PratikGupta114/Glider/Code_examples/Glider_v1.0/PlatformIO_projects/Line_Follower_Robot/src/Sensor.cpp

#include <stdint.h>
#include <stdbool.h>
#include <Arduino.h>

#include "GlobalVariables.h"
#include "PinDefinitions.h"
#include "Config.h"
#include "Wire.h"

bool sensorInitialized = false;

uint8_t shiftIn165(gpio_num_t dataPin, gpio_num_t clockPin, uint8_t bitOrder)
{
    uint8_t value = 0;
    uint8_t i;

    for (i = 0; i < 8; ++i)
    {
        uint8_t r = gpio_get_level(dataPin);
        if (bitOrder == LSBFIRST)
            value |= r << i;
        else
            value |= r << (7 - i);
        gpio_set_level(clockPin, 1);
        gpio_set_level(clockPin, 0);
    }

    return value;
}

uint8_t horizontalFlip(uint8_t byte)
{
    uint8_t flippedByte = 0x00;
    for (int i = 0; i < 4; i++)
    {
        uint8_t bs = (byte >> i) & 0x01;
        uint8_t be = (byte >> (7 - i)) & 0x01;
        flippedByte |= (bs << (7 - i)) | (be << i);
    }
    return flippedByte;
}

uint16_t getProcessedSensorData(uint8_t leftHalfPinState, uint8_t rightHalfPinState)
{
    leftHalfPinState = horizontalFlip(leftHalfPinState);
    rightHalfPinState = horizontalFlip(rightHalfPinState);

    uint16_t processedSensorData = leftHalfPinState << 8 | rightHalfPinState;

    return processedSensorData;
}

// returns a 2-byte data where each bit represent the state of each sensor
uint16_t getSensorReadings()
{
    uint16_t reading = 0x0000;

    if (!sensorInitialized)
    {
        gpio_config_t io_config;
        io_config.pin_bit_mask = (1 << DATA_PIN);
        io_config.mode = GPIO_MODE_INPUT;
        io_config.pull_up_en = GPIO_PULLUP_ENABLE;
        io_config.pull_down_en = GPIO_PULLDOWN_DISABLE;
        io_config.intr_type = GPIO_INTR_DISABLE;
        gpio_config(&io_config);

        io_config.pin_bit_mask = (1 << CLOCK_PIN | 1 << CLOCK_ENABLE_PIN | 1 << LOAD_PIN);
        io_config.mode = GPIO_MODE_OUTPUT;
        io_config.pull_up_en = GPIO_PULLUP_DISABLE;
        io_config.pull_down_en = GPIO_PULLDOWN_DISABLE;
        io_config.intr_type = GPIO_INTR_DISABLE;
        gpio_config(&io_config);
        delay(10);
        gpio_set_level(CLOCK_ENABLE_PIN, 1);

        sensorInitialized = true;
    }

    // Write pulse to load pin
    gpio_set_level(LOAD_PIN, 0);
    delayMicroseconds(50);
    gpio_set_level(LOAD_PIN, 1);
    delayMicroseconds(50);

    // Get data from 74HC165
    gpio_set_level(CLOCK_ENABLE_PIN, 0);
    uint8_t leftHalfPinState = shiftIn165(DATA_PIN, CLOCK_PIN, LSBFIRST);
    uint8_t rightHalfPinState = shiftIn165(DATA_PIN, CLOCK_PIN, LSBFIRST);
    gpio_set_level(CLOCK_ENABLE_PIN, 1);

    reading = getProcessedSensorData(leftHalfPinState, rightHalfPinState);
    reading &= 0b0011111111111100;

#if INVERSION_ENABLED == 1

    // Most inversion transitions occur at straight lines. This way, we can update the trackType variable
    // at straight line and not when the line is present towards the left / right side of the track.

    if (reading == 0b0000110000000000)
        trackType = WHITE_LINE_BLACK_TRACK;
    else if (reading == 0b0000011000000000 || reading == 0b0000111000000000 || reading == 0b0000111100000000 || reading == 0b0000010000000000)
        trackType = WHITE_LINE_BLACK_TRACK;
    if (reading == 0b0000011100000000)
        trackType = WHITE_LINE_BLACK_TRACK;
    else if (reading == 0b0000001110000000 || reading == 0b0000001100000000 || reading == 0b0000011110000000 || reading == 0b0000000100000000)
        trackType = WHITE_LINE_BLACK_TRACK;
    else if (reading == 0b0000000110000000)
        trackType = WHITE_LINE_BLACK_TRACK;
    else if (reading == 0b0000000111000000 || reading == 0b0000000011000000 || reading == 0b0000001111000000 || reading == 0b0000000010000000)
        trackType = WHITE_LINE_BLACK_TRACK;
    else if (reading == 0b0000000011100000)
        trackType = WHITE_LINE_BLACK_TRACK;
    else if (reading == 0b0000000001100000 || reading == 0b0000000001110000 || reading == 0b0000000011110000 || reading == 0b0000000000100000)
        trackType = WHITE_LINE_BLACK_TRACK;

    if (reading == 0b0011001111111100)
        trackType = BLACK_LINE_WHITE_TRACK;
    else if (reading == 0b0011100111111100 || reading == 0b0011000111111100 || reading == 0b0011101111111100)
        trackType = BLACK_LINE_WHITE_TRACK;
    else if (reading == 0b0011100011111100)
        trackType = BLACK_LINE_WHITE_TRACK;
    else if (reading == 0b0011110001111100 || reading == 0b0011110011111100 || reading == 0b0011111011111100)
        trackType = BLACK_LINE_WHITE_TRACK;
    else if (reading == 0b0011111001111100)
        trackType = BLACK_LINE_WHITE_TRACK;
    else if (reading == 0b0011111000111100 || reading == 0b0011111100111100 || reading == 0b0011111101111100)
        trackType = BLACK_LINE_WHITE_TRACK;
    else if (reading == 0b0011111100011100)
        trackType = BLACK_LINE_WHITE_TRACK;
    else if (reading == 0b0011111110011100 || reading == 0b0011111110001100 || reading == 0b0011111111011100)
        trackType = BLACK_LINE_WHITE_TRACK;

#endif

    // invert the sensor readings
    if (trackType == BLACK_LINE_WHITE_TRACK)
    {
        reading ^= 0b0011111111111100;
    }

    return reading;
}

// the following function calculates the error value in the following format
int getCalculatedError(int fallbackError)
{
    uint16_t sensorReading = getSensorReadings();
    int numeratorSum = 0, denominatorSum = 0;

    // Assuming that the the MSB represents the index 0 of the array (left to right)
    for (int i = 2; i <= (SENSOR_COUNT + 1); i++)
    {
        // Check the digital values at the ith bit
        uint16_t sensorValue = ((sensorReading & (1 << (15 - i))) >> (15 - i));
        numeratorSum += (i - 1) * 100 * (int)sensorValue;
        denominatorSum += sensorValue;
    }

    int error = fallbackError;
    if (denominatorSum != 0)
        error = ((numeratorSum / (denominatorSum * 50)) - (SENSOR_COUNT + 1));
    return error;
}

int isOutOfLine(uint16_t sensorReadings)
{
    // As the name suggests, contains most of sensor conditions
    // when the LFR is not out of line.
    uint16_t notOutOfLineConditions[] = {

        // 0b0001100000000000,
        0b0000110000000000,
        0b0000011000000000,
        0b0000001100000000,
        0b0000000110000000,
        0b0000000011000000,
        0b0000000001100000,
        0b0000000000110000,
        // 0b0000000000011000,
        // 0b0001110000000000,
        0b0000111000000000,
        0b0000011100000000,
        0b0000001110000000,
        0b0000000111000000,
        0b0000000011100000,
        0b0000000001110000,
        // 0b0000000000111000,
        0b0000100000000000,
        0b0000010000000000,
        0b0000001000000000,
        0b0000000100000000,
        0b0000000010000000,
        0b0000000001000000,
        0b0000000000100000,
        0b0000000000010000,
        // 0b0000011110000000,
        // 0b0000001111000000,
        // 0b0000000111100000,
        // 0b0000000011110000,
    };

    int n = sizeof(notOutOfLineConditions) / sizeof(uint16_t);

    for (int i = 0; i < n; i++)
    {
        if (sensorReadings == notOutOfLineConditions[i])
            return 0;
    }

    // return (sensorReadings == 0b0000000000000000) ? 1 : 0;

    return 1;
}
