PratikGupta114/Glider/Code_examples/Glider_v1.0/PlatformIO_projects/Line_Follower_Robot/src/MotorControl.h

#pragma once

#ifndef MOTORCONTROL_H
#define MOTORCONTROL_H

void moveStraight(int leftMotorSpeed, int rightMotorSpeed);
void turnCCW(int leftMotorSpeed, int rightMotorSpeed);
void turnCW(int leftMotorSpeed, int rightMotorSpeed);
void shortBrake(int durationMillis);
void stop();

#endif
